aliasmeum/RFVplotter-DrawingRobot/RFVplotterParts/PlotterHeadParts/StepFiles/RFVplotter-BeltConnectorArm-v1_0.step

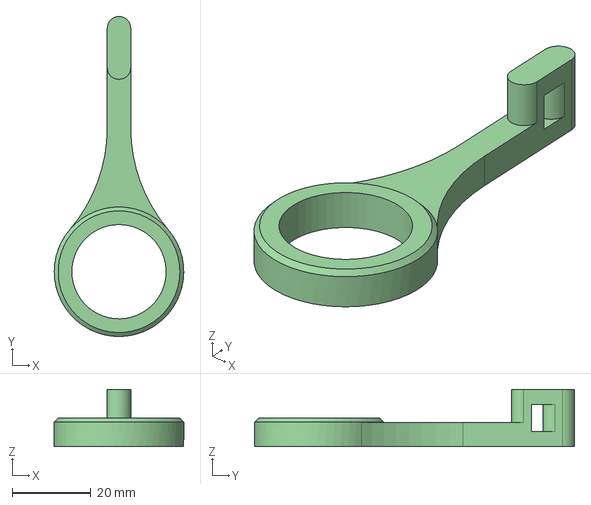
[picture p12: CAD file, 2022-10-16]
RFVplotterParts/PlotterHeadParts/StepFiles/RFVplotter-BeltConnectorArm-v1_0.step
33.0 x 81.5 x 14.6 mm
