aliasmeum/RFVplotter-DrawingRobot/RFVplotterParts/PlotterHeadParts/MeshFiles/RFVplotter-PenLifterBody-v1_0.3mf

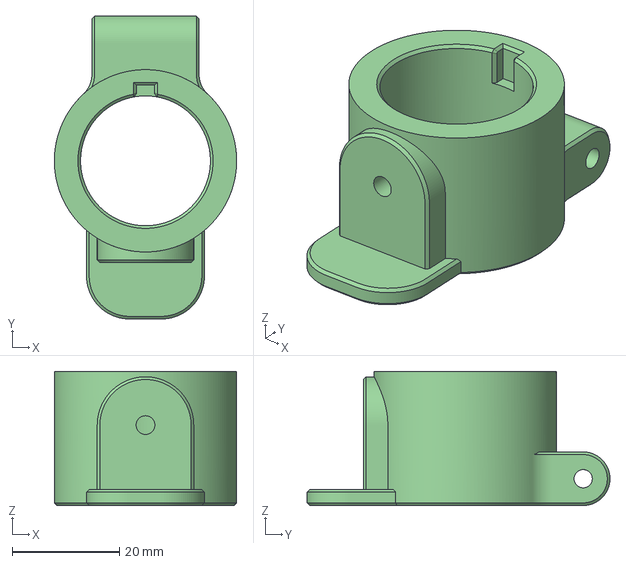
[picture p13: CAD file, 2022-10-16]
RFVplotterParts/PlotterHeadParts/MeshFiles/RFVplotter-PenLifterBody-v1_0.3mf
34.0 x 56.5 x 25.0 mm
