aliasmeum/RFVplotter-DrawingRobot/RFVplotterParts/PlotterHeadParts/StepFiles/RFVplotter-PenHolder10p5mm-v1_0.step

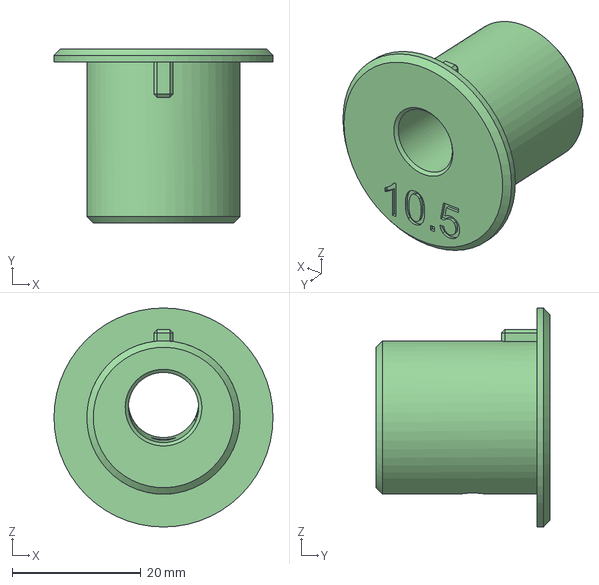
[picture p14: CAD file, 2022-10-16]
RFVplotterParts/PlotterHeadParts/StepFiles/RFVplotter-PenHolder10p5mm-v1_0.step
34.0 x 27.0 x 34.0 mm
