aliasmeum/RFVplotter-DrawingRobot/RFVplotterParts/PlotterHeadParts/StepFiles/RFVplotter-DistancePlate-v1_0.step

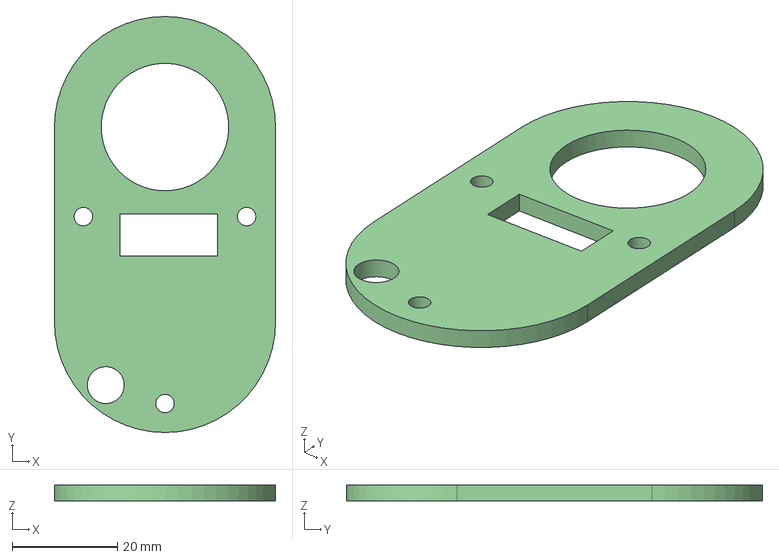
[picture p15: CAD file, 2022-10-16]
RFVplotterParts/PlotterHeadParts/StepFiles/RFVplotter-DistancePlate-v1_0.step
42.0 x 79.0 x 3.00 mm
