aliasmeum/RFVplotter-DrawingRobot/RFVplotterParts/PlotterHeadParts/MeshFiles/RFVplotter-FrontPlate-v1_0.3mf

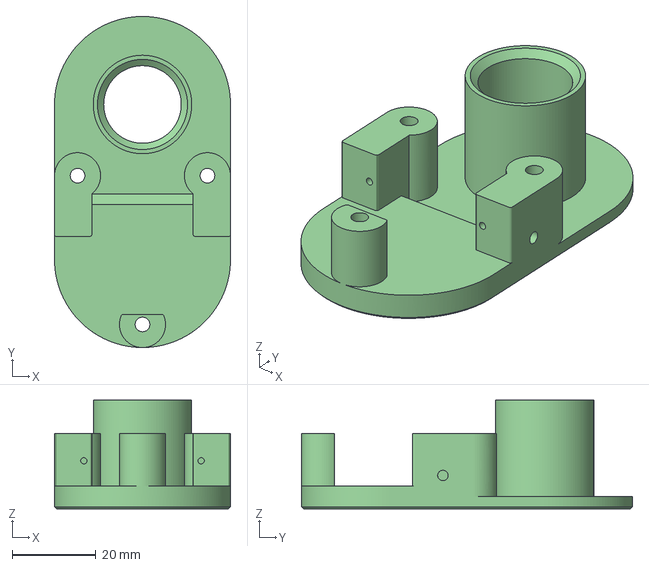
[picture p16: CAD file, 2022-10-16]
RFVplotterParts/PlotterHeadParts/MeshFiles/RFVplotter-FrontPlate-v1_0.3mf
42.0 x 79.0 x 26.0 mm
