aliasmeum/RFVplotter-DrawingRobot/RFVplotterParts/PlotterHeadParts/StepFiles/RFVplotter-FrontPlate-v1_0.step

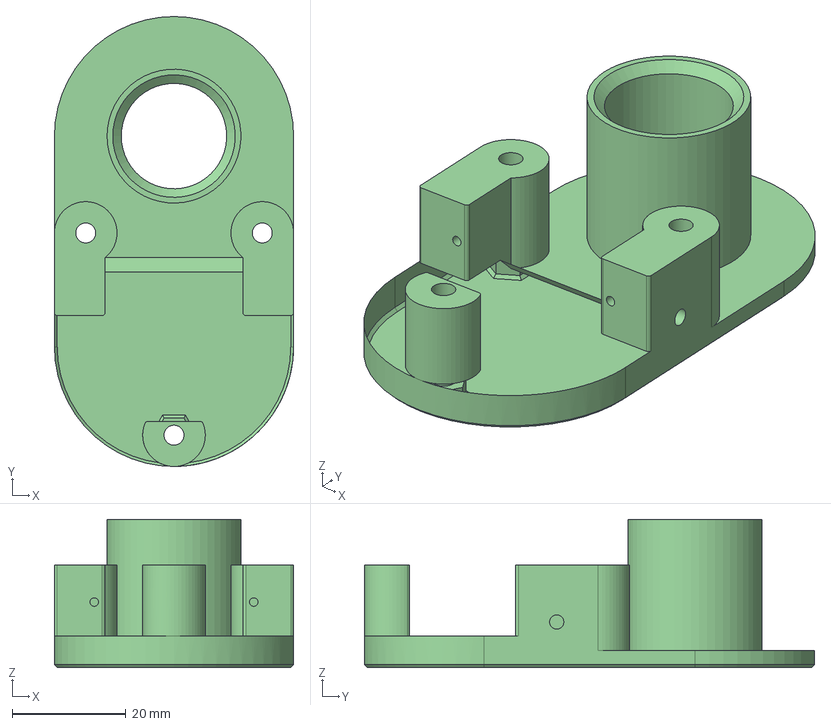
[picture p17: CAD file, 2022-10-16]
RFVplotterParts/PlotterHeadParts/StepFiles/RFVplotter-FrontPlate-v1_0.step
42.0 x 79.0 x 26.0 mm
