aliasmeum/RFVplotter-DrawingRobot/RFVplotterParts/PlotterHeadParts/MeshFiles/RFVplotter-BeltConnectorArm-v1_0.3mf

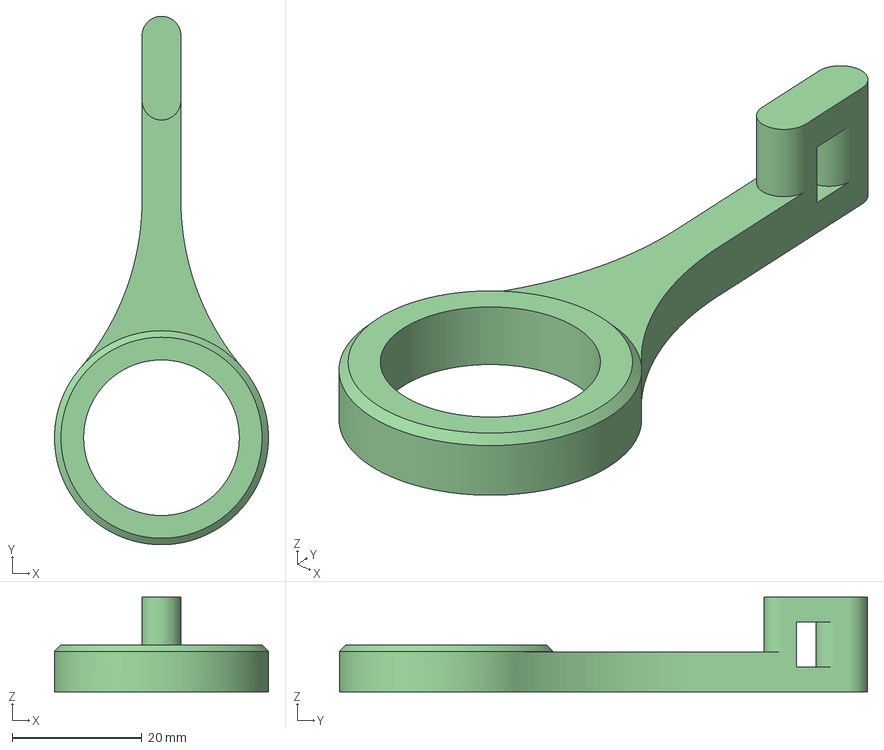
[picture p18: CAD file, 2022-10-16]
RFVplotterParts/PlotterHeadParts/MeshFiles/RFVplotter-BeltConnectorArm-v1_0.3mf
33.0 x 81.5 x 14.6 mm
