aliasmeum/RFVplotter-DrawingRobot/RFVplotterParts/PlotterHeadParts/MeshFiles/RFVPlotter-Riser10mm-v1_0.3mf

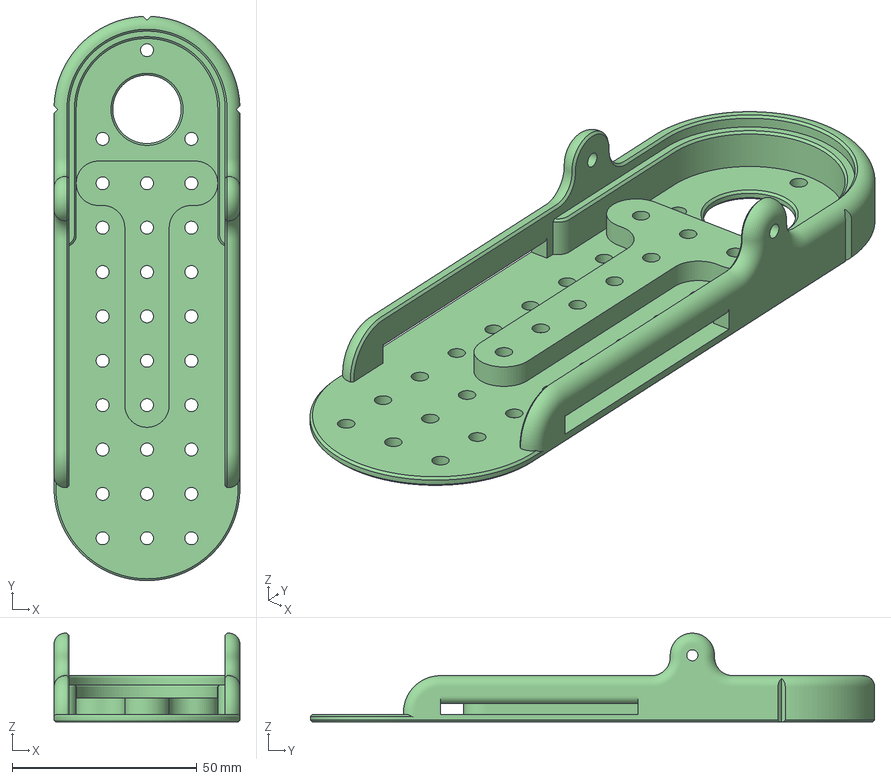
[picture p19: CAD file, 2022-10-16]
RFVplotterParts/PlotterHeadParts/MeshFiles/RFVPlotter-Riser10mm-v1_0.3mf
50.3 x 152.6 x 24.0 mm
